riissitsurana4/keyboard_V1/images/Screenshot 2026-07-17 at 3.09.30 AM.png

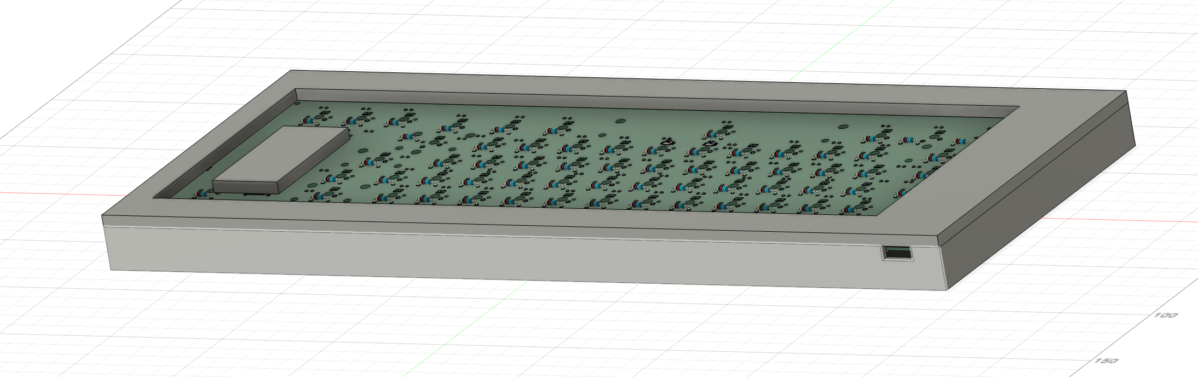
images/Screenshot 2026-07-17 at 3.09.30 AM.png
